Ashet-Technologies/Home-Computer/Hardware/Case/models/usb_a_2_0_fem_vert_a-e.stl

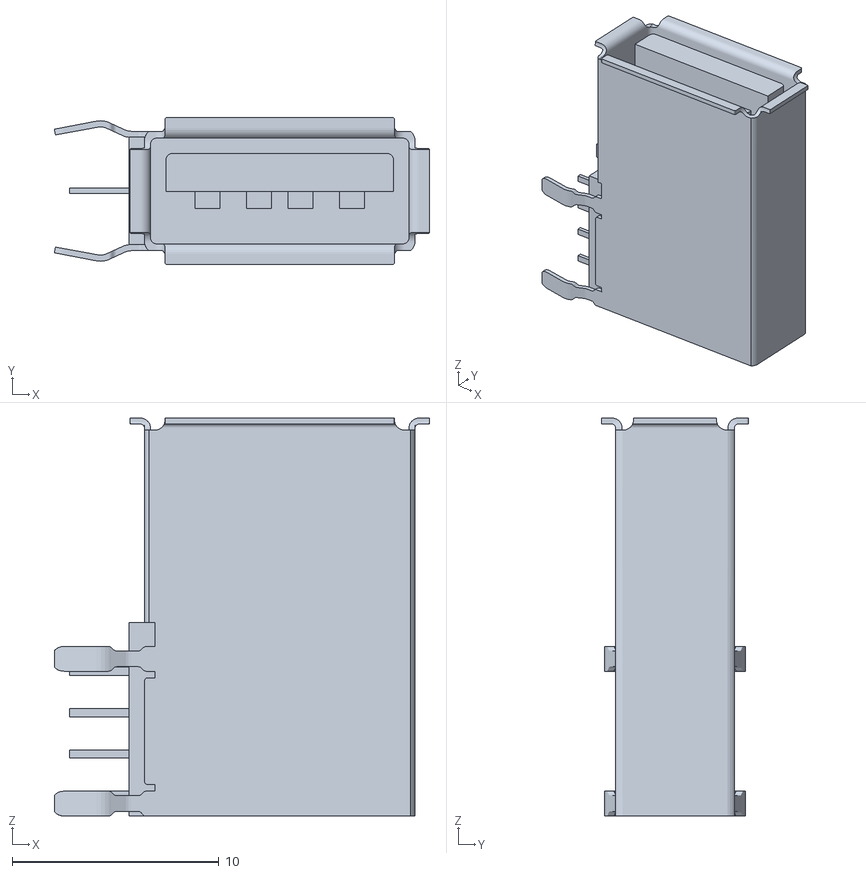
[picture p20: CAD file, 2024-12-29]
Hardware/Case/models/usb_a_2_0_fem_vert_a-e.stl
18.2 x 7.12 x 19.3
