Ashet-Technologies/Home-Computer/Hardware/Case/models/pinheader_12x2_302-R241-56544.stl

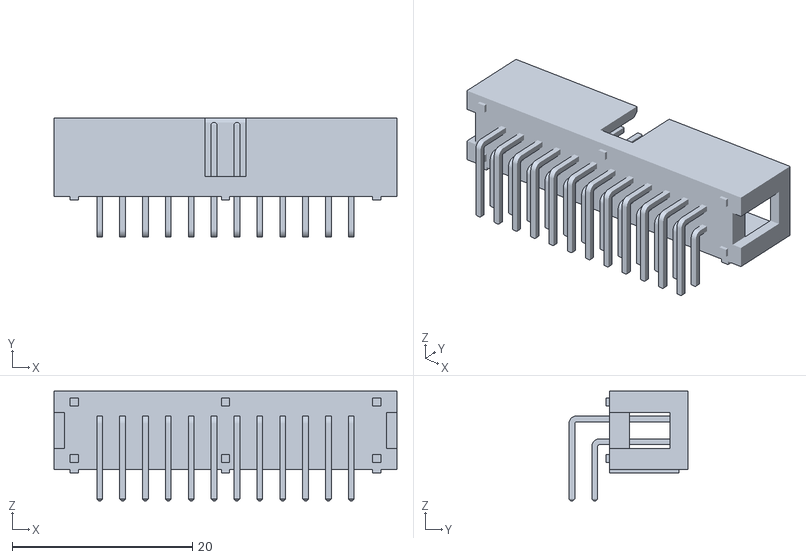
[picture p21: CAD file, 2024-12-29]
Hardware/Case/models/pinheader_12x2_302-R241-56544.stl
38.1 x 13.2 x 12.2
