Ashet-Technologies/Home-Computer/Hardware/Case/models/microsw_vert_2x_141_TL2243.stl

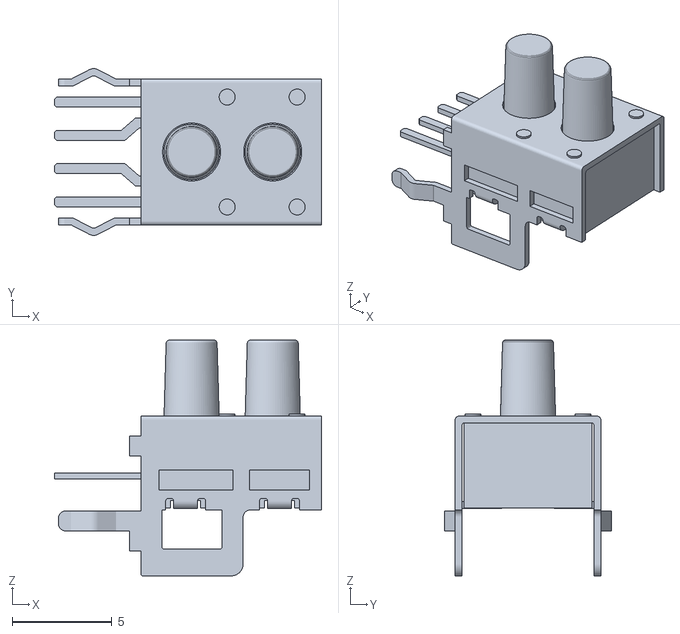
[picture p22: CAD file, 2024-12-29]
Hardware/Case/models/microsw_vert_2x_141_TL2243.stl
13.4 x 8.35 x 11.8
