Ashet-Technologies/Home-Computer/Hardware/Case/models/cinch_rcj-041.stl

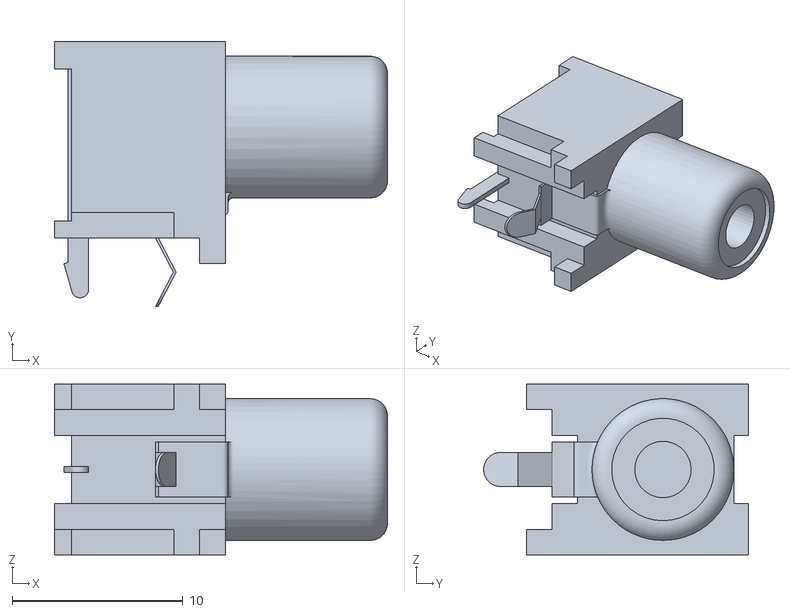
[picture p23: CAD file, 2024-12-29]
Hardware/Case/models/cinch_rcj-041.stl
19.5 x 15.5 x 10.0
