Ashet-Technologies/Home-Computer/Hardware/Case/models/hdmi_fem_2010418.stl

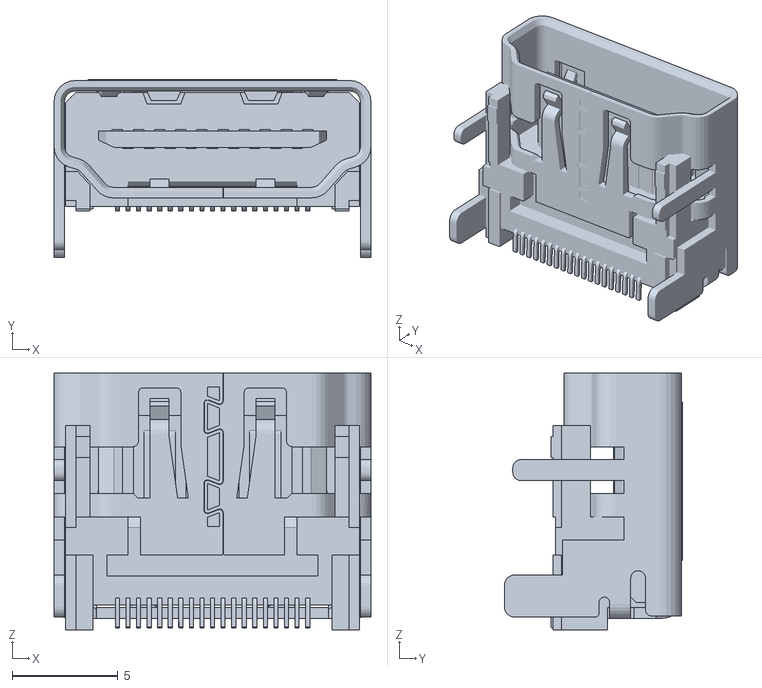
[picture p24: CAD file, 2024-12-29]
Hardware/Case/models/hdmi_fem_2010418.stl
15.0 x 8.45 x 12.1
