Ashet-Technologies/Home-Computer/Hardware/Case/models/sub-de15-90deg_fem_6740971p.stl

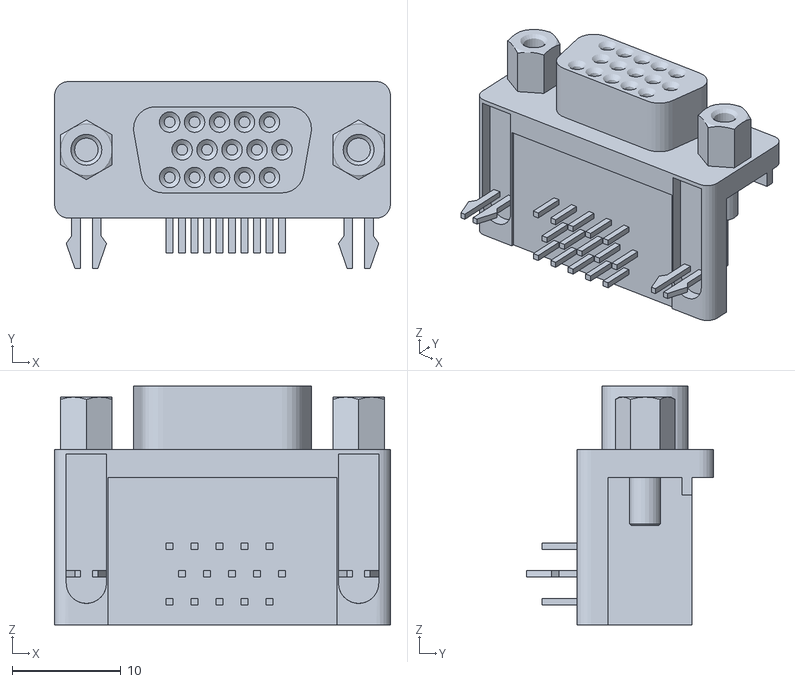
[picture p25: CAD file, 2024-12-29]
Hardware/Case/models/sub-de15-90deg_fem_6740971p.stl
30.8 x 17.2 x 21.9
