Ashet-Technologies/Home-Computer/Hardware/Case/models/usb_c_fem_201267-0005.stl

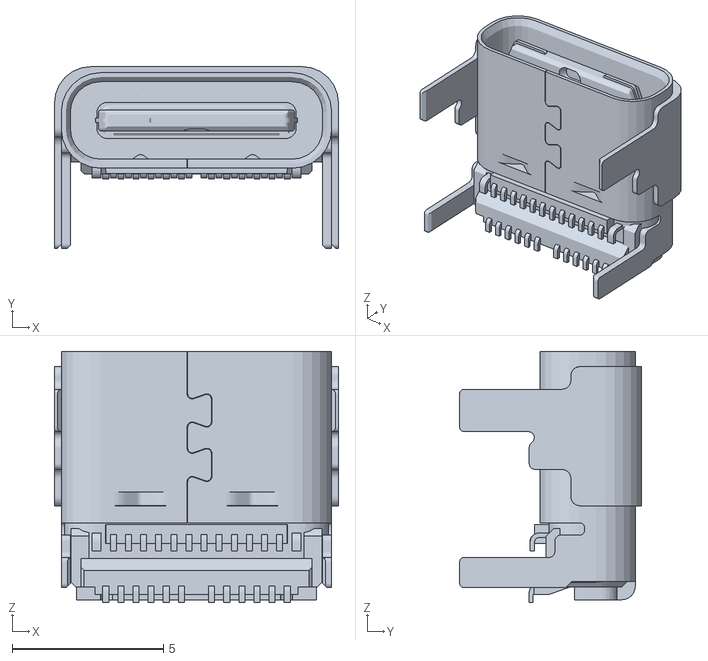
[picture p27: CAD file, 2024-12-29]
Hardware/Case/models/usb_c_fem_201267-0005.stl
9.39 x 6.01 x 8.30
