Ashet-Technologies/Home-Computer/Hardware/Case/models/usb_a_2_0_fem_48258-0001.stl

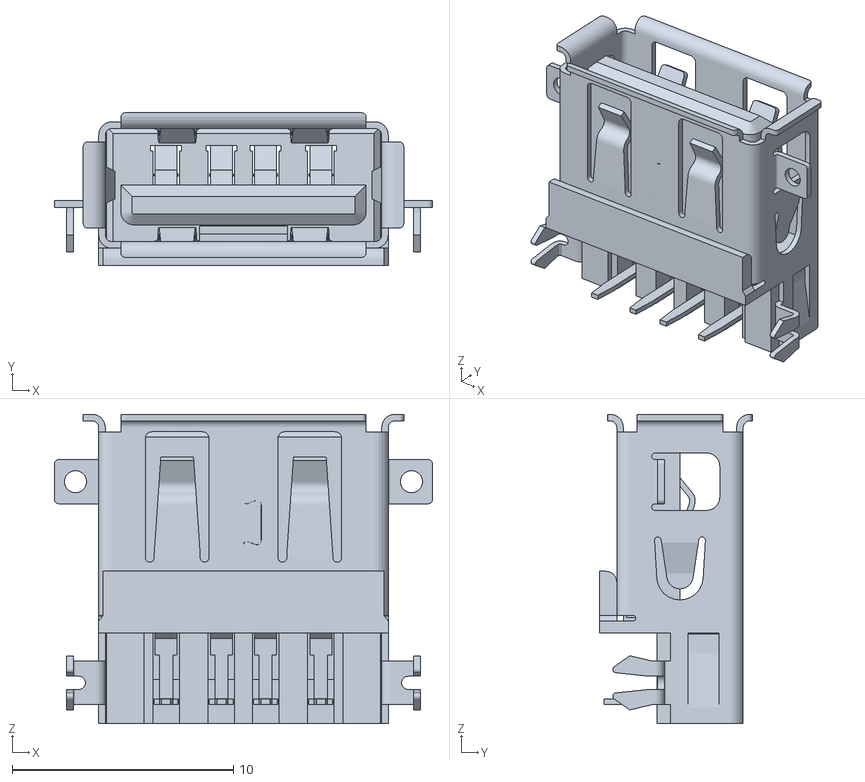
[picture p28: CAD file, 2024-12-29]
Hardware/Case/models/usb_a_2_0_fem_48258-0001.stl
17.1 x 6.90 x 14.0
