Ashet-Technologies/Home-Computer/Hardware/Case/models/sub-de9-90deg_fem_1216782.stl

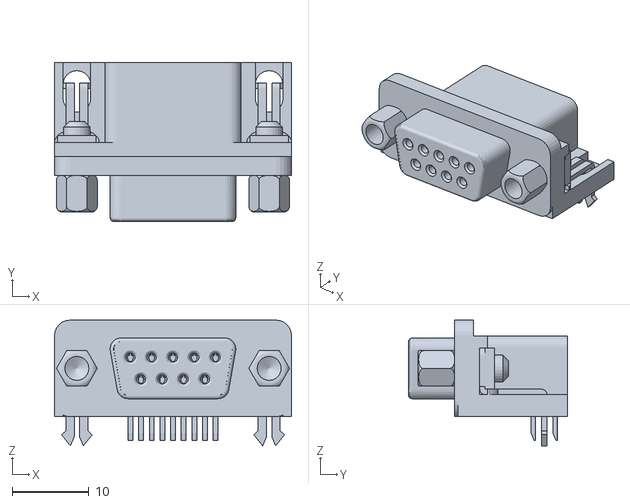
[picture p29: CAD file, 2024-12-29]
Hardware/Case/models/sub-de9-90deg_fem_1216782.stl
30.8 x 20.7 x 16.3
