Ashet-Technologies/Home-Computer/Hardware/Case/models/dvi_fem_74320-1007.stl

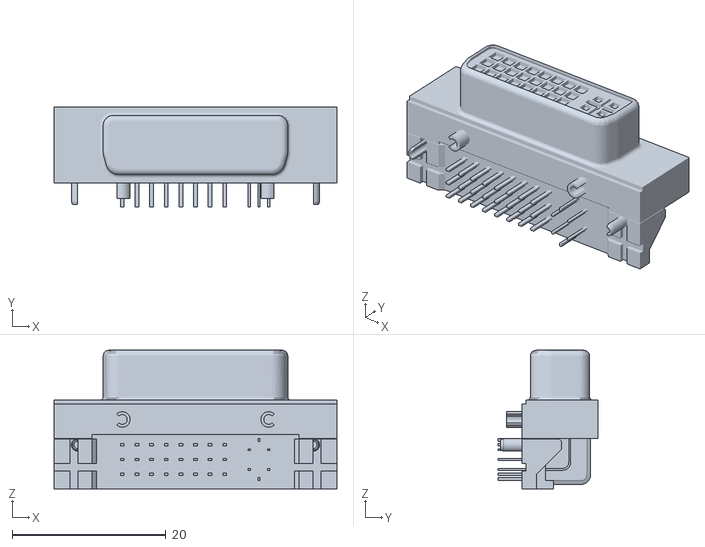
[picture p30: CAD file, 2024-12-29]
Hardware/Case/models/dvi_fem_74320-1007.stl
36.8 x 13.0 x 18.0
