Ashet-Technologies/Home-Computer/Hardware/Case/models/jack_3_5_fem_8051665.stl

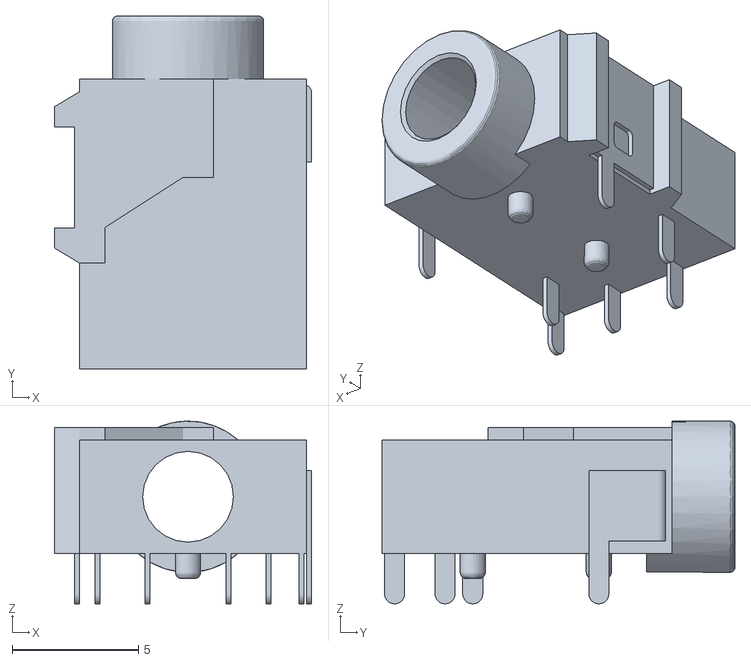
[picture p31: CAD file, 2024-12-29]
Hardware/Case/models/jack_3_5_fem_8051665.stl
10.2 x 14.0 x 7.25
