Ashet-Technologies/Home-Computer/Hardware/Interconnector/Interconnector.scad

linear_extrude(0.5) {
    import("Export/Interconnector-B_Cu.dxf"); 
}
