Ashet-Technologies/Home-Computer/Hardware/Case/models/models.scad

module conn_sub_de_9_fem()
{
    // https://www.traceparts.com/en/product/rs-group-103mm-9-way-90deg-dsub-pcb-socket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
    translate([ 0, 7.5, 6.3 ]) import("sub-de9-90deg_fem_1216782.stl");
}

module conn_sub_de_9_male()
{
    // https://www.traceparts.com/en/product/rs-group-103mm-9w-header-90deg-dsub-connector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
    translate([ 0, 7.5, 6.3 ]) import("sub-de9-90deg_male_1216780.stl");
}

module conn_sub_de_15_fem()
{
    // https://www.traceparts.com/en/product/rs-group-15w-hd-dsub-ra-pcb-socket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
    translate([ 0, 0, 6.25 ]) rotate(90, [ 1, 0, 0 ]) import("sub-de15-90deg_fem_6740971p.stl");
}

module conn_usb_a_2_0_fem()
{
    // https://www.traceparts.com/en/product/rs-components-48258-series-number-right-angle-panel-mount-version-20-type-a-usb-connector-receptacle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
    translate([ 0, 6.8, 3.5 ]) rotate(90, [ 1, 0, 0 ]) import("usb_a_2_0_fem_48258-0001.stl");
}

module conn_usb_c_fem()
{
    // https://www.traceparts.com/en/product/rs-components-2012670005-female-usb-c-connector-right-angle-surface-mount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
    translate([ -5.4, 3.5, -3.2 ]) rotate(90, [ 1, 0, 0 ]) import("usb_c_fem_201267-0005.stl");
}

module conn_hdmi_fem()
{
    // https://www.traceparts.com/en/product/rs-group-10-hdmi-ra-header-assy-im-type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
    translate([ 0, 12, 7.4 ]) rotate(90, [ 1, 0, 0 ]) import("hdmi_fem_2010418.stl");
}

module conn_dvi_fem()
{
    // https://www.traceparts.com/en/product/rs-components-female-right-angle-dvi-connector-29-way-3a-40-v-ac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
    translate([ 0, 0.5, 5 ]) rotate(90, [ 1, 0, 0 ]) import("dvi_fem_74320-1007.stl");
}

module conn_jack_3_5mm_fem()
{
    // https://www.traceparts.com/en/product/rs-group-35mm-jack-socket-pcb4-pole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
    translate([ 0, 0, 2.4 ]) rotate(180, [ 0, 0, 1 ]) import("jack_3_5_fem_8051665.stl");
}

module display_oled_128x64_0_96_in()
{
    // https://grabcad.com/library/modeling-oled-screen-128x64-0-91in-by-espacio-maker-1
    translate([ 0, 0, 13 ]) rotate(90, [ 1, 0, 0 ]) import("Tela OLed 128x64 v15.stl");
}

module conn_rj45()
{
    // https://www.traceparts.com/en/product/rs-components-blinded-lightpipe-89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
    translate([ 0, 7.5, 6.4 ]) rotate(90, [ 1, 0, 0 ]) import("rj45_43860-0016.stl");
}

module conn_cinch_female()
{
    // https://www.sameskydevices.com/product/resource/digikey3dmodel/rcj-041
    rotate(180, [ 0, 0, 1 ]) translate([ -5, -10, -3.8 ]) rotate(90, [ 0, 0, 1 ]) rotate(90, [ 1, 0, 0 ])
        import("cinch_rcj-041.stl");
}

module conn_usb_a_2_0_vert_fem()
{
    // https://www.traceparts.com/en/product/rs-components-assmann-wsw-through-hole-type-a-usb-connector-receptacle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
    translate([ 0, -0.3, 7.5 ]) rotate(90, [ 1, 0, 0 ]) rotate(90, [ 0, 0, 1 ]) import("usb_a_2_0_fem_vert_a-e.stl");
}

module conn_din_6pin_45322_fem()
{
    // https://www.digikey.de/de/products/detail/te-connectivity-amp-connectors/5212045-1/813421
    translate([ 0, 0, 10 ]) rotate(90, [ 1, 0, 0 ]) import("din_6pin_5212045-1.stl");
}

module conn_pinheader_12x2_90deg_border()
{
    // https://www.digikey.de/de/products/detail/on-shore-technology-inc/302-R241/2794248
    translate([ 0, 8.5, 4.5 ]) rotate(180, [ 0, 0, 1 ]) import("pinheader_12x2_302-R241-56544.stl");
}

module conn_microswitch_2x_vert()
{
    // https://www.digikey.de/de/products/detail/e-switch/TL2243/1794126
    translate([ 0, 4.5, 5 ]) rotate(90, [ 1, 0, 0 ]) rotate(90, [ 0, 0, 1 ]) import("microsw_vert_2x_141_TL2243.stl");
}

module dev_rpi_4b()
{
    // https://www.printables.com/model/727545-raspberry-pi-4/files
    translate([ 0, 42.5, 0.9 ]) rotate(-90, [ 0, 0, 1 ]) rotate(90, [ 1, 0, 0 ]) import("raspberrypi-model-4b.stl");
}

module dev_ikea_vaerdera()
{
    // https://www.ikea.com/de/de/p/vaerdera-becher-weiss-10277366/
    $fs = 0.1;
    $fa = 10;
    hs1 = 30;
    hs2 = 75;
    db = 50;
    ds = 65;
    dt = 80;
    t = 2;

    hw = 15;
    hd = 60;
    ht = 5;
    hvo = 35;

    difference()
    {
        union()
        {
            cylinder(h = hs1, d1 = db, d2 = ds);
            translate([ 0, 0, hs1 ]) cylinder(h = hs2, d1 = ds, d2 = dt);

            // handle:
            translate([ -hw / 2, -40, hvo + hd / 2 ]) rotate(5, [ 1, 0, 0 ]) rotate(90, [ 0, 1, 0 ])
                scale([ 1, 0.5, 1 ]) difference()
            {
                cylinder(h = hw, d = hd);
                translate([ 0, 0, -hw ]) cylinder(h = 3 * hw, d = hd - 2 * ht);
            }
        }
        translate([ 0, 0, t ]) cylinder(h = hs1 - t + 0.01, d1 = db - 2 * t, d2 = ds - 2 * t);
        translate([ 0, 0, hs1 - 0.001 ]) cylinder(h = hs2 + t + 0.01, d1 = ds - 2 * t, d2 = dt - 2 * t);
    }
}

module case_rm2095l(fp = true,bot=false)
{
    // https://www.hammfg.com/electronics/small-case/plastic/rm2
    if(bot)
    {
        import("rm2095l_bottom_part.stl");
    }
    else if (fp)
    {
        import("rm2095l.stl");
    }
    else
    {
        import("rm2095l_no_frontplate.stl");
    }
}

module case_rm2095l_fp()
{
    import("rm2095l_frontplate.stl");
}

module conn_pcie_x4()
{
    translate([ 0, 0, 0]) rotate(90, [ 0, 0, 1 ]) rotate(90, [ 1, 0, 0 ]) import("pcie_x4_10018784-10201TLF.stl");
}

module screw_m2_5_4mm()
{
    import("10294970.stl");
}
