Ashet-Technologies/Home-Computer/Hardware/Case/models/preview.scad

use <models.scad>


module preview()
{
    color("red") cube([0.25,100,0.25],true);
    children();
}

module parts_demo()
{
    translate([-100,-50,-3]) color("#cccccc") cube([1000,100,3]); 
    translate([-100,0,0]) color("blue") cube([1000,50,0.1]); 

    translate([-70,0,0]) preview() dev_ikea_vaerdera();

    translate([0,0,0])   preview() conn_sub_de_9_fem();
    translate([40,0,0])  preview() conn_sub_de_9_male();
    translate([80,0,0])  preview() conn_sub_de_15_fem();
    translate([110,0,0]) preview() conn_usb_a_2_0_fem();
    translate([130,0,0]) preview() conn_usb_c_fem();
    translate([150,0,0]) preview() conn_hdmi_fem();
    translate([180,0,0]) preview() conn_dvi_fem();
    translate([210,0,0]) preview() conn_jack_3_5mm_fem();
    translate([240,0,0]) preview() display_oled_128x64_0_96_in();
    translate([270,0,0]) preview() conn_rj45();
    translate([290,0,0]) preview() conn_cinch_female();
    translate([310,0,0]) preview() conn_usb_a_2_0_vert_fem();
    translate([330,0,0]) preview() conn_din_6pin_45322_fem();
    translate([370,0,0]) preview() conn_pinheader_12x2_90deg_border();
    translate([400,0,0]) preview() conn_microswitch_2x_vert();

    translate([440,0,0]) preview() dev_rpi_4b();

    translate([480,0,0]) preview() conn_pcie_x4();
}


parts_demo();

// case_rm2095l();
